tm-miha/Upcyling-stool-Precious-hocker-IF-Demo/res/conf/README.md

# README `res/conf/`

Configuration & settings files, e.g. 3D printer settings, log settings, ...
