tm-miha/Upcyling-stool-Precious-hocker-IF-Demo/src/elec/README.md

# README `src/elec/`

Electronic "blueprints" - Schemas & PCBs
