tm-miha/Upcyling-stool-Precious-hocker-IF-Demo/res/assets/media/img/regenholz_precious-hocker_02-gehrung.jpg

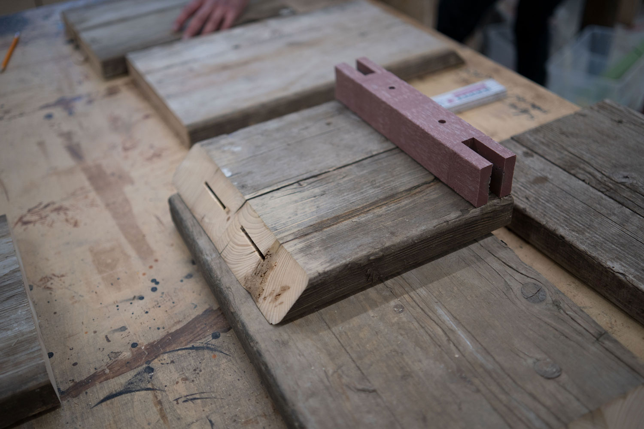
res/assets/media/img/regenholz_precious-hocker_02-gehrung.jpg
