tm-miha/Upcyling-stool-Precious-hocker-IF-Demo/res/assets/media/img/regenholz_precious-hocker_03-lamello.jpg

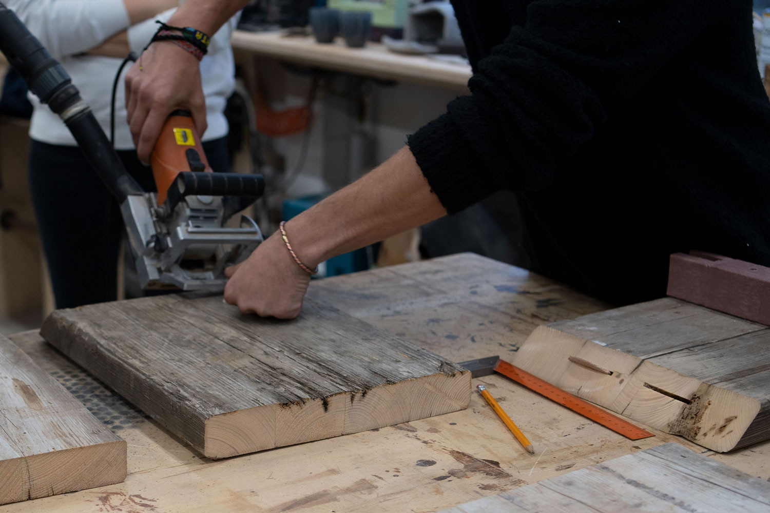
res/assets/media/img/regenholz_precious-hocker_03-lamello.jpg
