tm-miha/Upcyling-stool-Precious-hocker-IF-Demo/res/assets/media/img/regenholz_precious-hocker_04-innenseite-schleifen.jpg

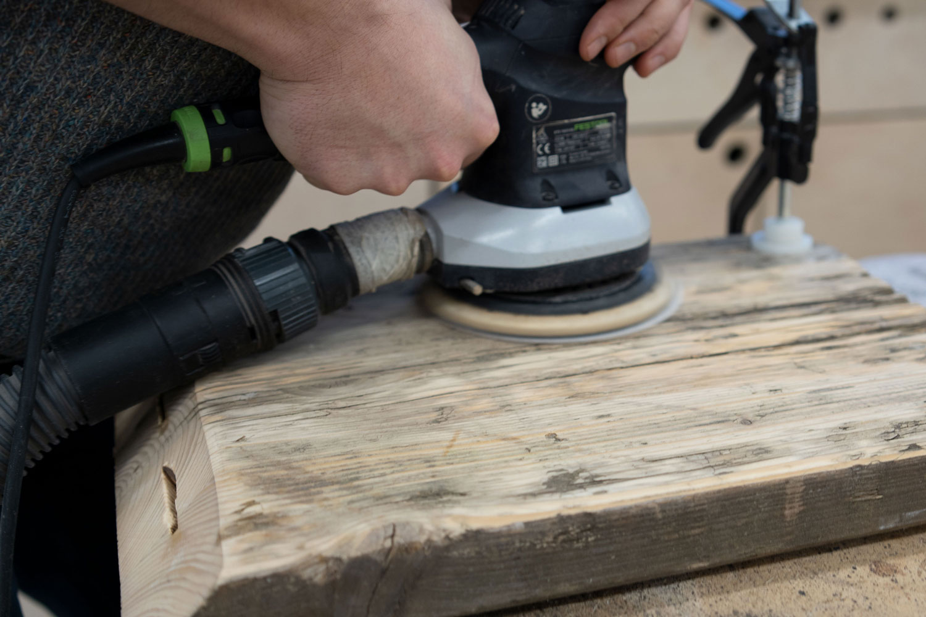
res/assets/media/img/regenholz_precious-hocker_04-innenseite-schleifen.jpg
