tm-miha/Upcyling-stool-Precious-hocker-IF-Demo/res/assets/media/img/regenholz_precious-hocker_06-verleimen.jpg

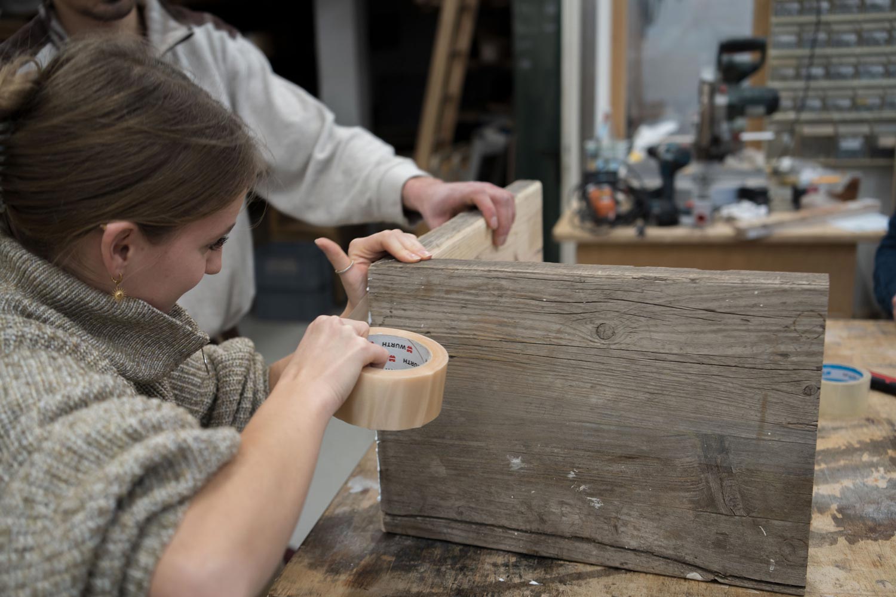
res/assets/media/img/regenholz_precious-hocker_06-verleimen.jpg
