tm-miha/Upcyling-stool-Precious-hocker-IF-Demo/res/assets/media/img/regenholz_precious-hocker_07-verleimen.jpg

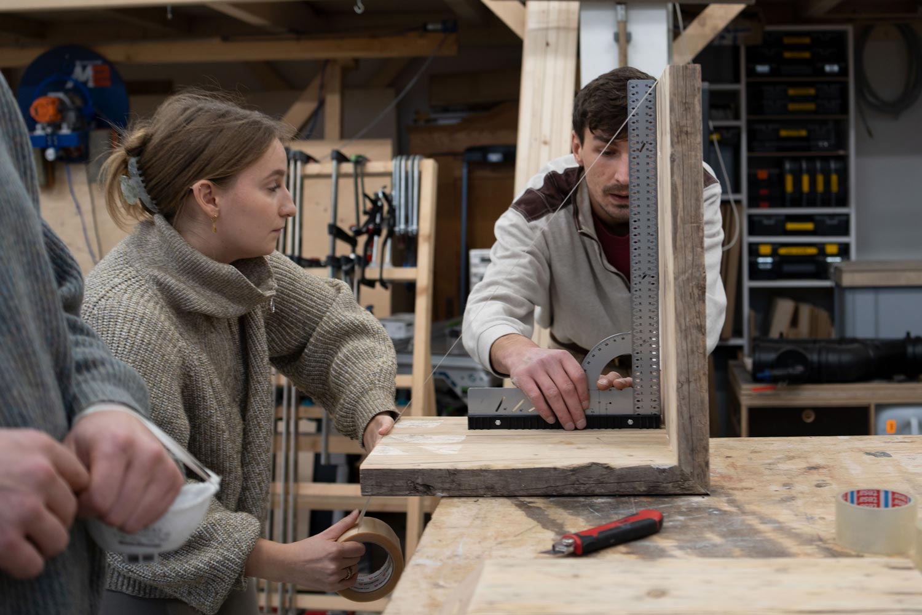
res/assets/media/img/regenholz_precious-hocker_07-verleimen.jpg
