tm-miha/Upcyling-stool-Precious-hocker-IF-Demo/res/assets/media/img/regenholz_precious-hocker_08-kantenbrechen.jpg

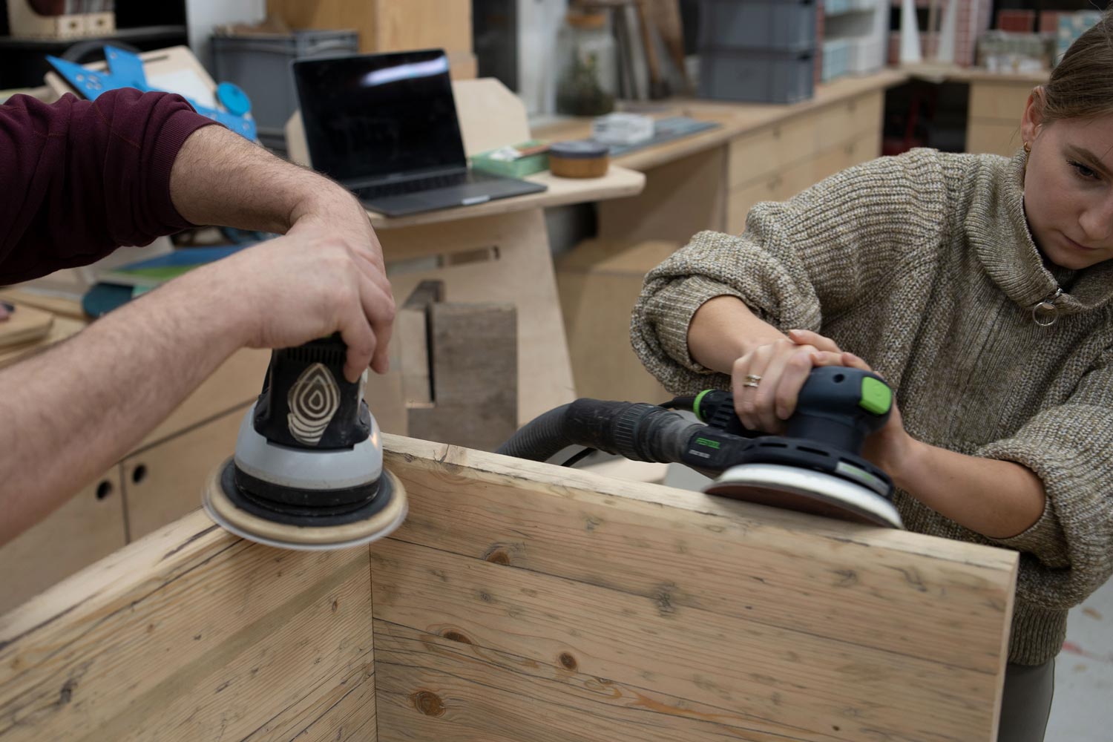
res/assets/media/img/regenholz_precious-hocker_08-kantenbrechen.jpg
