tm-miha/Upcyling-stool-Precious-hocker-IF-Demo/res/assets/media/img/regenholz_precious-hocker_09-aussenseite-schleifen.jpg

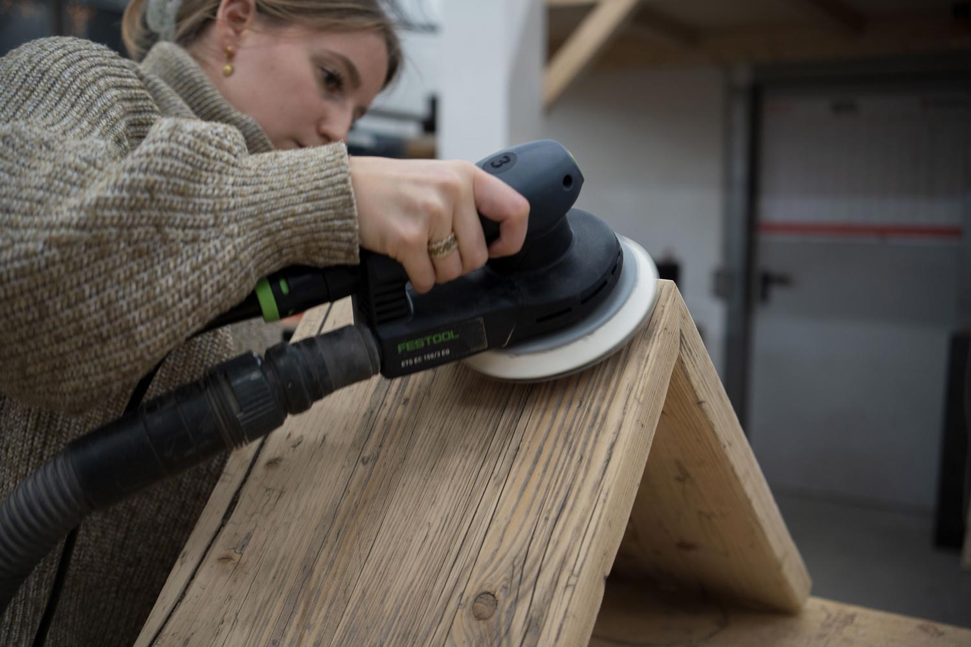
res/assets/media/img/regenholz_precious-hocker_09-aussenseite-schleifen.jpg
