tm-miha/Upcyling-stool-Precious-hocker-IF-Demo/res/assets/media/img/regenholz_precious-hocker_12-zuschnitt-plastikbalken.jpg

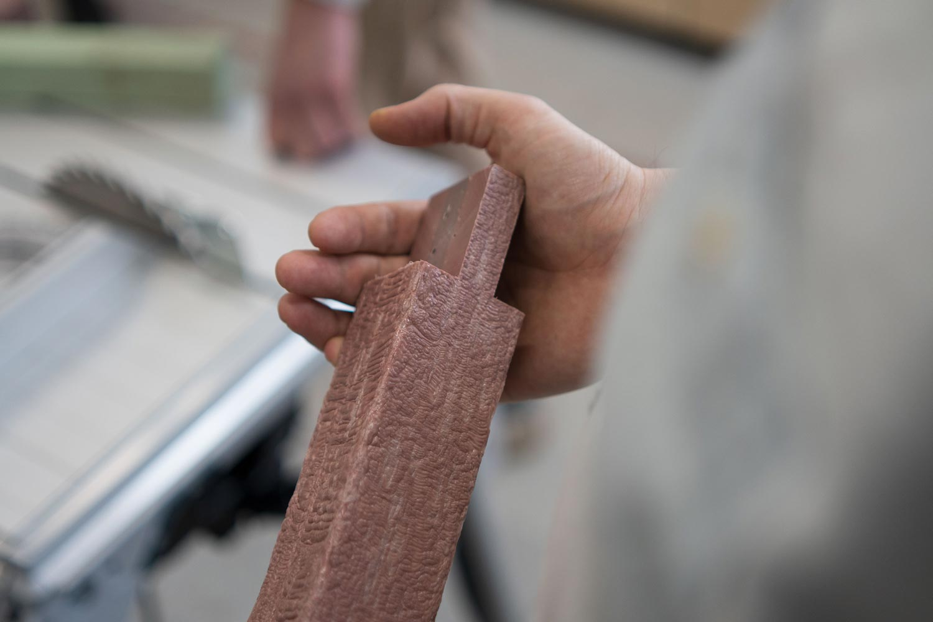
res/assets/media/img/regenholz_precious-hocker_12-zuschnitt-plastikbalken.jpg
