tm-miha/Upcyling-stool-Precious-hocker-IF-Demo/res/assets/media/img/regenholz_precious-hocker_15-verbindungen-bohren.jpg

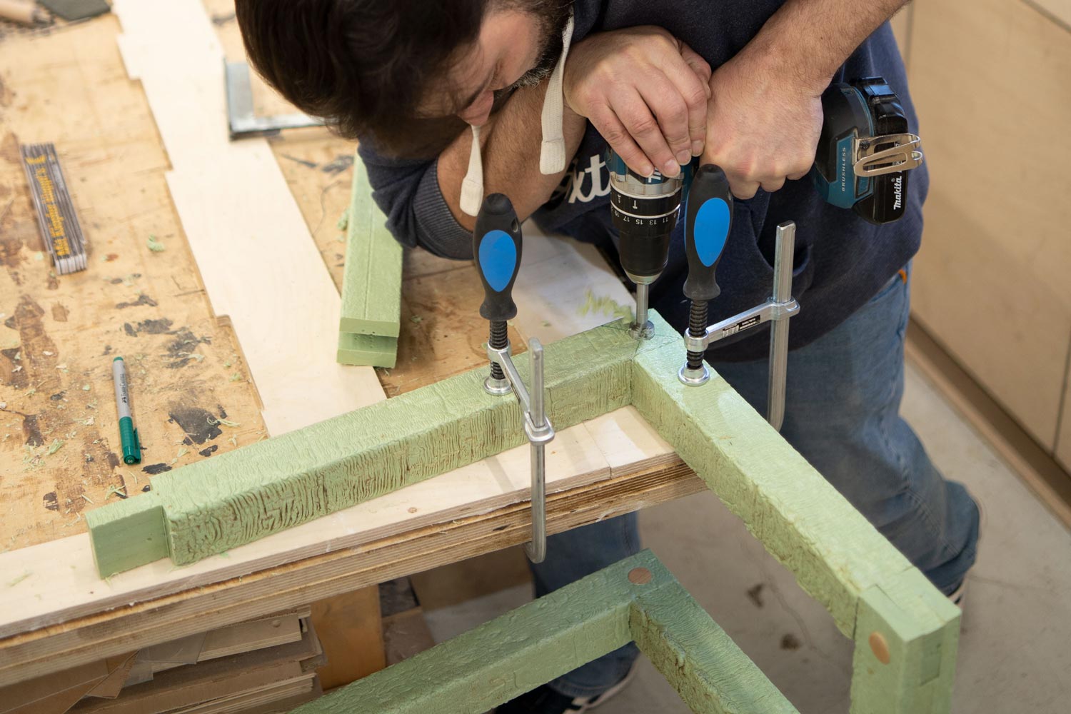
res/assets/media/img/regenholz_precious-hocker_15-verbindungen-bohren.jpg
