tm-miha/Upcyling-stool-Precious-hocker-IF-Demo/res/assets/media/img/regenholz_precious-hocker_16-schraubloecher-vorbohren.jpg

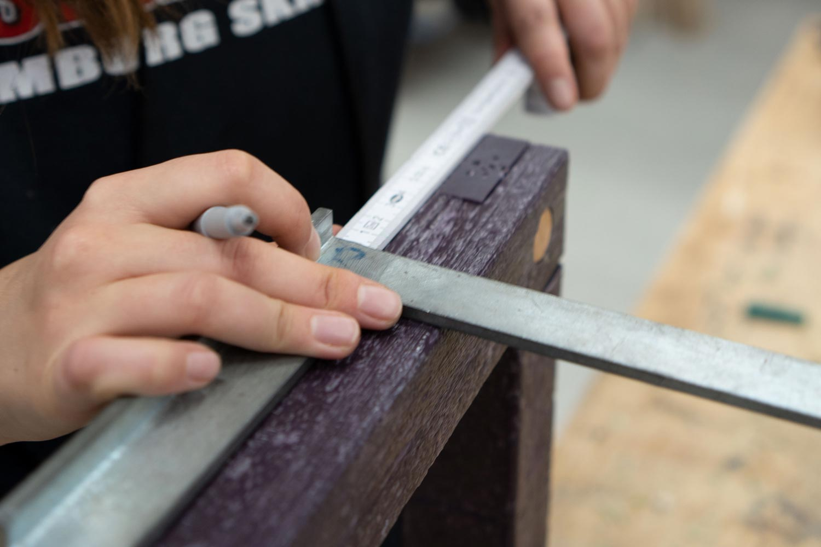
res/assets/media/img/regenholz_precious-hocker_16-schraubloecher-vorbohren.jpg
