tm-miha/Upcyling-stool-Precious-hocker-IF-Demo/res/assets/media/img/regenholz_precious-hocker_18-rundstaebe-saegen.jpg

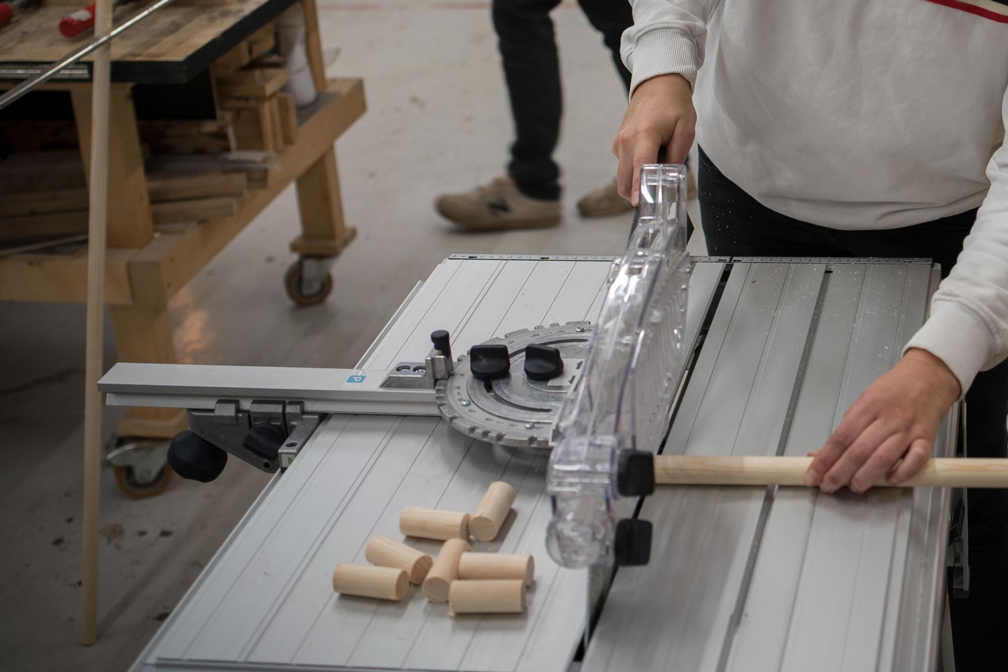
res/assets/media/img/regenholz_precious-hocker_18-rundstaebe-saegen.jpg
