tm-miha/Upcyling-stool-Precious-hocker-IF-Demo/res/assets/media/img/regenholz_precious-hocker_21-gestell-bauen.jpg

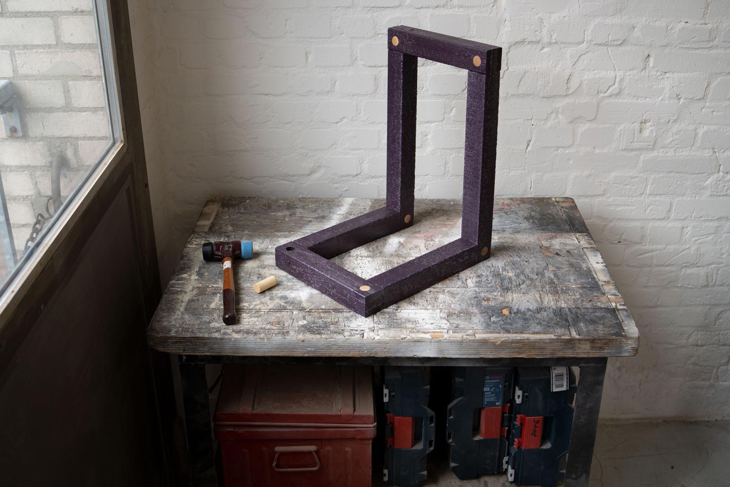
res/assets/media/img/regenholz_precious-hocker_21-gestell-bauen.jpg
