tm-miha/Upcyling-stool-Precious-hocker-IF-Demo/res/assets/media/img/regenholz_precious-hocker_23-zusammenbau.jpg

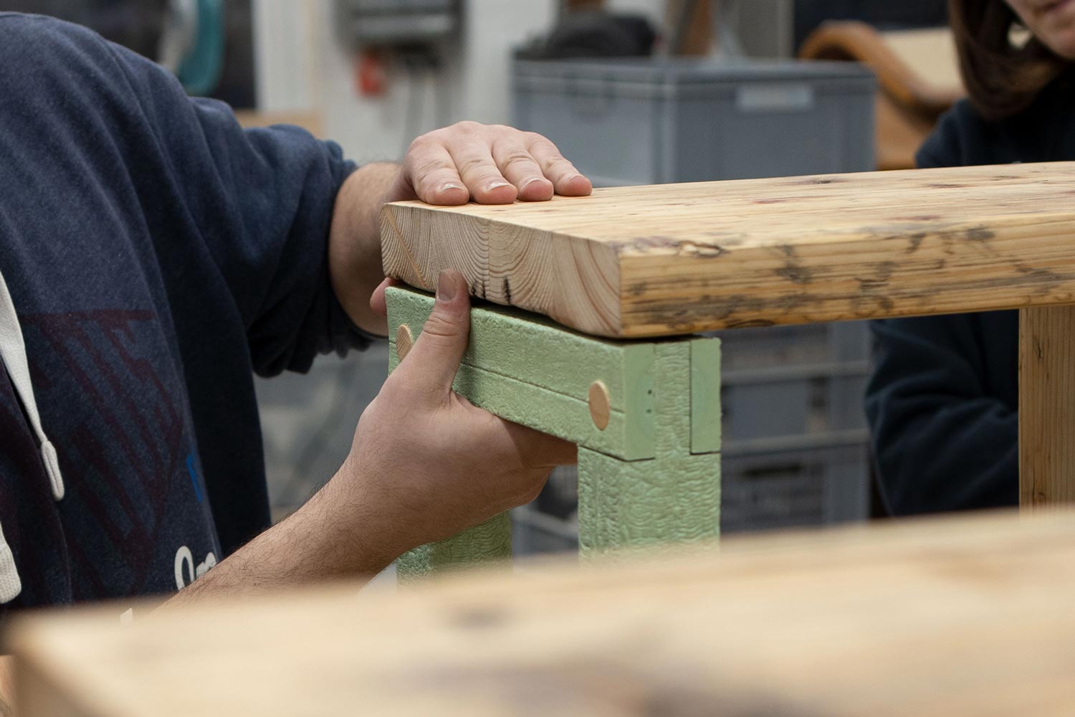
res/assets/media/img/regenholz_precious-hocker_23-zusammenbau.jpg
