tm-miha/Upcyling-stool-Precious-hocker-IF-Demo/res/assets/media/img/regenholz_precious-hocker_24-zusammenbau.jpg

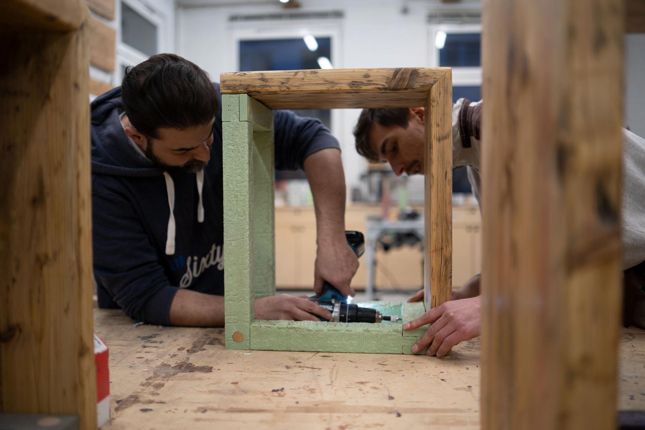
res/assets/media/img/regenholz_precious-hocker_24-zusammenbau.jpg
