tm-miha/Upcyling-stool-Precious-hocker-IF-Demo/res/assets/media/img/regenholz_precious-hocker_dimensions-01.jpg

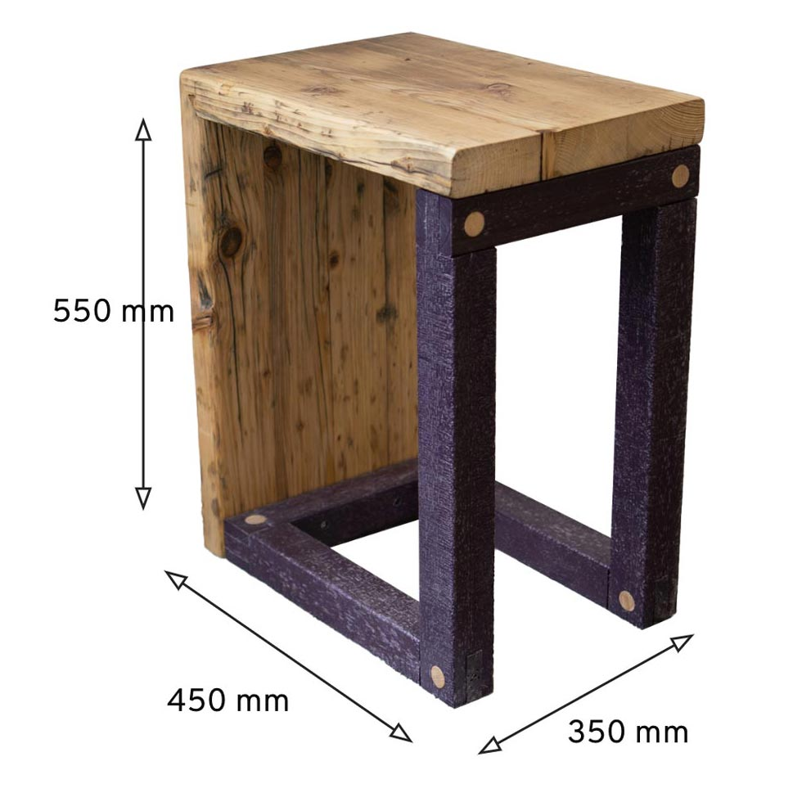
res/assets/media/img/regenholz_precious-hocker_dimensions-01.jpg
