tm-miha/Upcyling-stool-Precious-hocker-IF-Demo/res/assets/media/img/screenshot-1.jpg

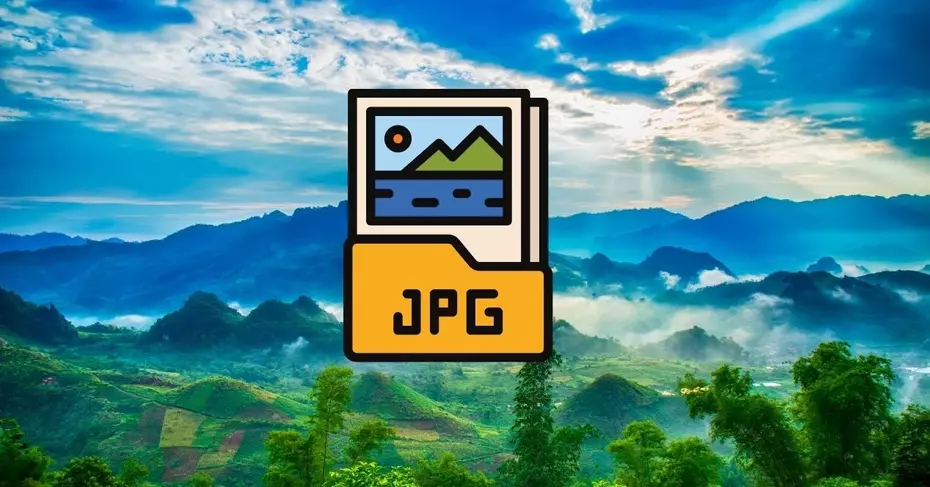
res/assets/media/img/screenshot-1.jpg
